formtapez/ZigUP/Pictures/top.jpg

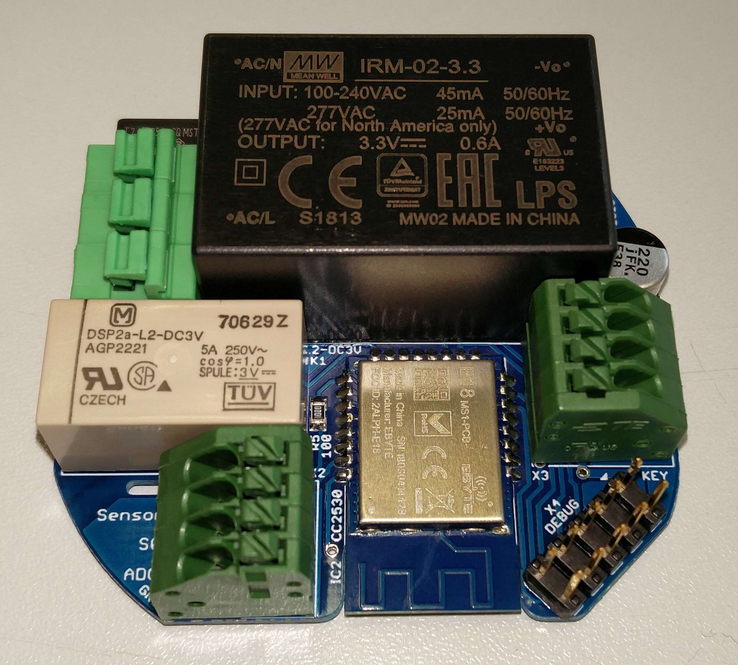
Pictures/top.jpg
