formtapez/ZigUP/src/ZigUP/Source/bitmasks.h

#define b00000000 0x00
#define b00000001 0x01
#define b00000010 0x02
#define b00000011 0x03
#define b00000100 0x04
#define b00000101 0x05
#define b00000110 0x06
#define b00000111 0x07
#define b00001000 0x08
#define b00001001 0x09
#define b00001010 0x0a
#define b00001011 0x0b
#define b00001100 0x0c
#define b00001101 0x0d
#define b00001110 0x0e
#define b00001111 0x0f
#define b00010000 0x10
#define b00010001 0x11
#define b00010010 0x12
#define b00010011 0x13
#define b00010100 0x14
#define b00010101 0x15
#define b00010110 0x16
#define b00010111 0x17
#define b00011000 0x18
#define b00011001 0x19
#define b00011010 0x1a
#define b00011011 0x1b
#define b00011100 0x1c
#define b00011101 0x1d
#define b00011110 0x1e
#define b00011111 0x1f
#define b00100000 0x20
#define b00100001 0x21
#define b00100010 0x22
#define b00100011 0x23
#define b00100100 0x24
#define b00100101 0x25
#define b00100110 0x26
#define b00100111 0x27
#define b00101000 0x28
#define b00101001 0x29
#define b00101010 0x2a
#define b00101011 0x2b
#define b00101100 0x2c
#define b00101101 0x2d
#define b00101110 0x2e
#define b00101111 0x2f
#define b00110000 0x30
#define b00110001 0x31
#define b00110010 0x32
#define b00110011 0x33
#define b00110100 0x34
#define b00110101 0x35
#define b00110110 0x36
#define b00110111 0x37
#define b00111000 0x38
#define b00111001 0x39
#define b00111010 0x3a
#define b00111011 0x3b
#define b00111100 0x3c
#define b00111101 0x3d
#define b00111110 0x3e
#define b00111111 0x3f
#define b01000000 0x40
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
#define b11110100 0xf4
#define b11110101 0xf5
#define b11110110 0xf6
#define b11110111 0xf7
#define b11111000 0xf8
#define b11111001 0xf9
#define b11111010 0xfa
#define b11111011 0xfb
#define b11111100 0xfc
#define b11111101 0xfd
#define b11111110 0xfe
#define b11111111 0xff
