formtapez/ZigUP/src/ZigUP/Source/interrupts.c

#include <stdio.h>
#include "onboard.h"
#include "ZComDef.h"
#include "bitmasks.h"
#include "delay.h"
#include "ds18b20.h"
#include "uart.h"
#include "global.h"
#include "ws2812.h"
#include "led.h"
#include "interrupts.h"
#include "zcl_zigup.h"
#include "utils.h"

#pragma vector=P0INT_VECTOR 
__interrupt void IRQ_S0(void)
{
  if (P0IFG & (1<<6))	// Interrupt flag for P0.6 (S0)?
  {
    S0++;
    UART_String("[INT] S0!");
    
    // Clear interrupt flags
    P0IFG &= ~(1<<6);	// Clear Interrupt flag for P0.6 (S0)
    IRCON &= ~(1<<5);	// Clear Interrupt flag for Port 0
  }
}

#pragma vector=P1INT_VECTOR 
__interrupt void IRQ_KEY(void)
{
  if (P1IFG & (1<<3))	// Interrupt flag for P1.3 (KEY)?
  {
    // debounce
    _delay_ms(20);
    if (!P1_3) // still pressed?
    {
      Relais(!STATE_LIGHT);
      UART_String("[INT] KEY!");
      
      // detection for longer keypress
      uint8 counter = 0;
      while (!P1_3 && counter < 100)
      {
        _delay_ms(50);
        counter++;
      }
      if (counter >= 100) FactoryReset();
      
      // update measurements (only the quick stuff, to stay responsive)
      Measure_QuickStuff();
      
      // report states
      zclZigUP_Reporting(REPORT_REASON_KEY);      
    }
    
    // Clear interrupt flags
    P1IFG &= ~(1<<3);	// Clear Interrupt flag for P1.3 (KEY)
    IRCON2 &= ~(1<<3);	// Clear Interrupt flag for Port 1
  }
}

#pragma vector=P2INT_VECTOR 
__interrupt void IRQ_DIGIN(void)
{
  if (P2IFG & (1<<0))	// Interrupt flag for P2.0 (Dig-In)?
  {
    // debounce
    _delay_ms(20);
    if (!P2_0) // still pressed?
    {
      DIG_IN = P2_0;
      UART_String("[INT] Dig-In!");
      
      // detection for longer keypress
      uint8 counter = 0;
      while (!P1_3 && counter < 100)
      {
        _delay_ms(50);
        counter++;
      }
      if (counter >= 100) FactoryReset();
      
      // update measurements (only the quick stuff, to stay responsive)
      Measure_QuickStuff();
      
      // report states
      zclZigUP_Reporting(REPORT_REASON_DIGIN);  
    }
    
    // Clear interrupt flags
    P2IFG &= ~(1<<0);	// Clear Interrupt flag for P2.0 (Dig-In)
    IRCON2 &= ~(1<<0);	// Clear Interrupt flag for Port 2
  }
}
